vibr77/AppleIIDiskIIStm32F411/doc/controllercard/Apple-1-616-130-12-Apple-II-LIron-3-5-Unidisk-Floppy-Disk-Drive-Interface-Card_94765__16121.jpg

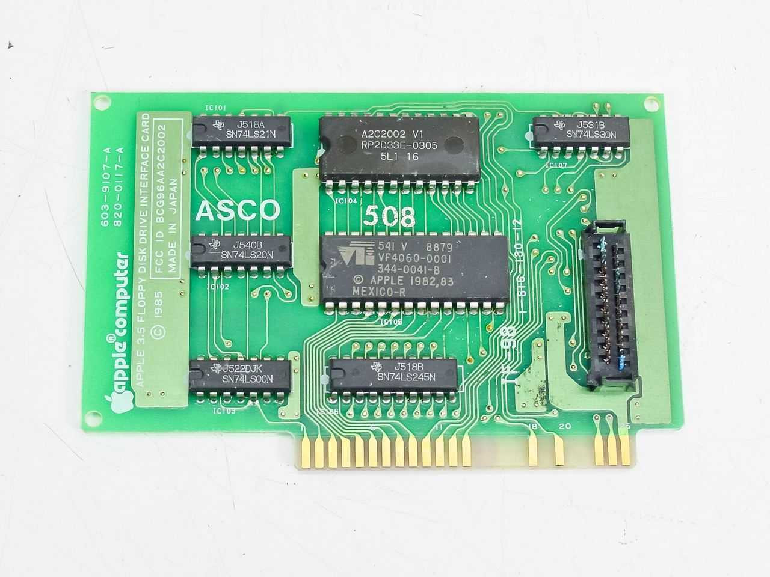
doc/controllercard/Apple-1-616-130-12-Apple-II-LIron-3-5-Unidisk-Floppy-Disk-Drive-Interface-Card_94765__16121.jpg
