vibr77/AppleIIDiskIIStm32F411/doc/controllercard/Disk-II-interface.jpg

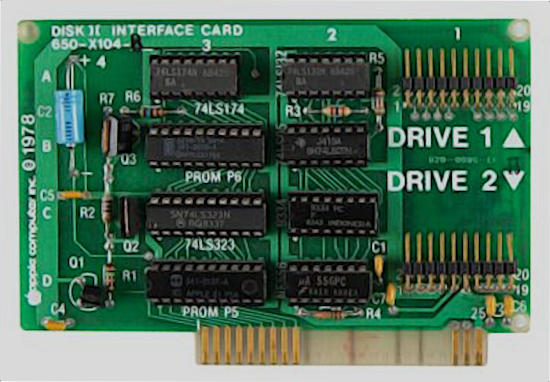
doc/controllercard/Disk-II-interface.jpg
