vibr77/AppleIIDiskIIStm32F411/doc/controllercard/grapplerminus.jpg

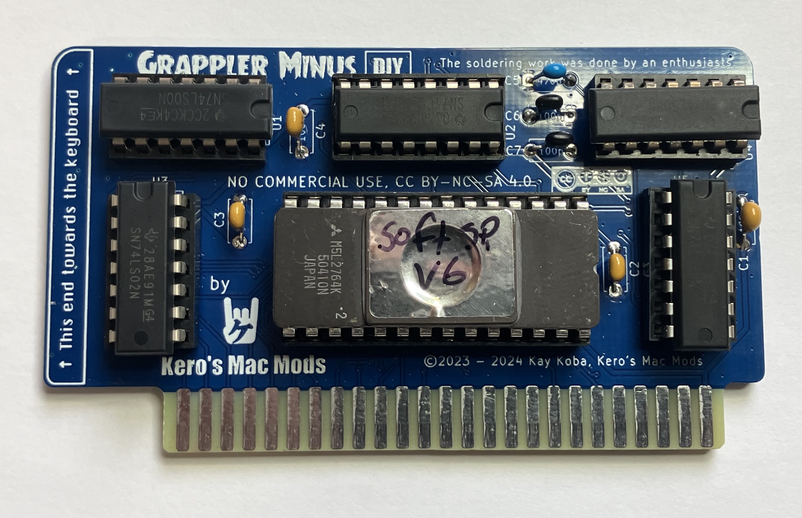
doc/controllercard/grapplerminus.jpg
