vibr77/AppleIIDiskIIStm32F411/doc/controllercard/yellowstone-270.png

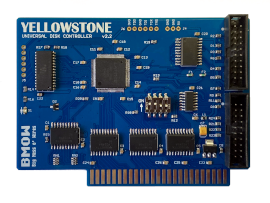
doc/controllercard/yellowstone-270.png
