vibr77/AppleIIDiskIIStm32F411/documentation/resources/IMG_1727-retouched-transparent_1_e6c90fae-1d42-45fb-9aed-f4f2a7baa5a6_1500x.png.webp

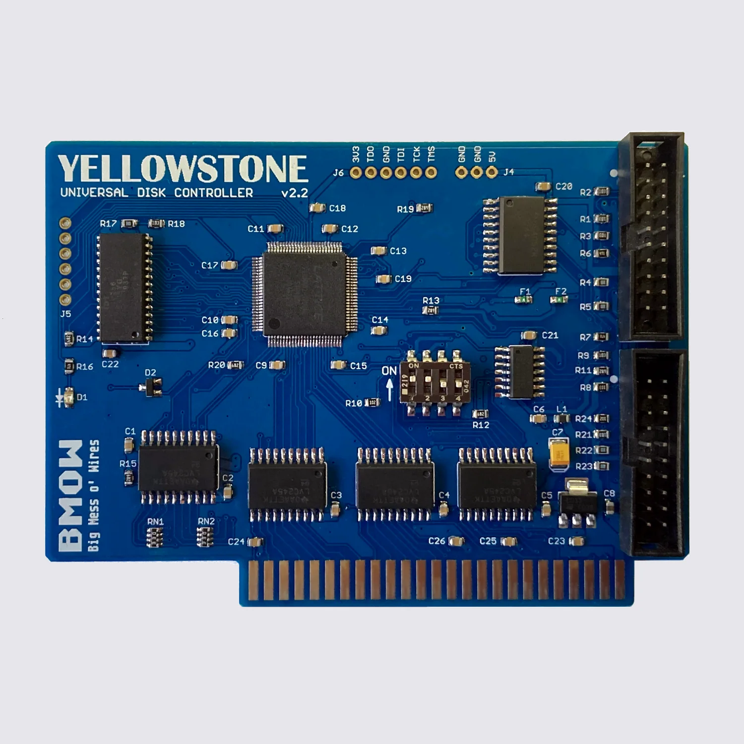
documentation/resources/IMG_1727-retouched-transparent_1_e6c90fae-1d42-45fb-9aed-f4f2a7baa5a6_1500x.png.webp
