vibr77/AppleIIDiskIIStm32F411/hardware/12085_buzzer/Image1.png

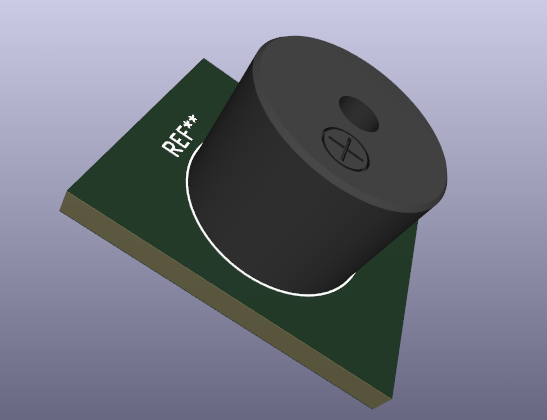
hardware/12085_buzzer/Image1.png
