vibr77/AppleIIDiskIIStm32F411/resources/CASE.jpeg

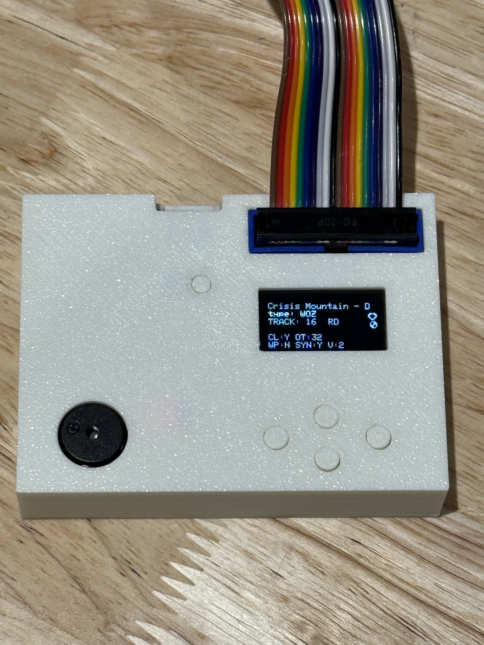
resources/CASE.jpeg
