vibr77/AppleIIDiskIIStm32F411/resources/PCB_REV_1_FILELST.jpeg

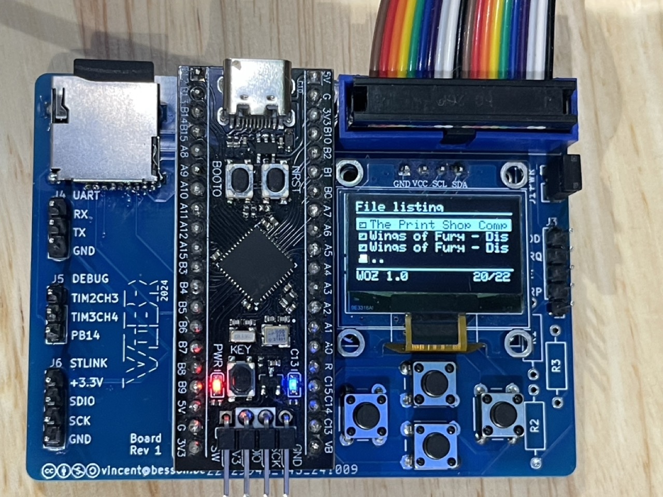
resources/PCB_REV_1_FILELST.jpeg
