vibr77/AppleIIDiskIIStm32F411/resources/STLINK.jpg

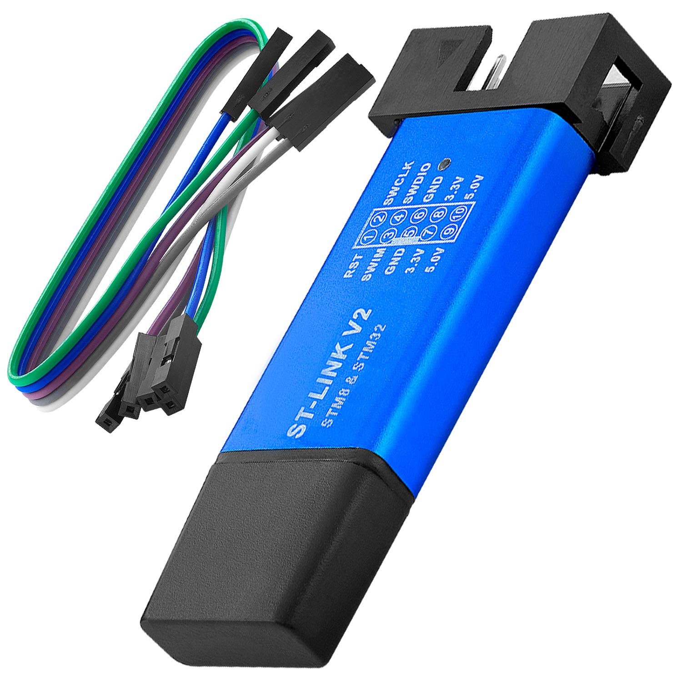
resources/STLINK.jpg
