vibr77/AppleIIDiskIIStm32F411/3DPrintCase/v4/SmartDiskII top v4.3mf

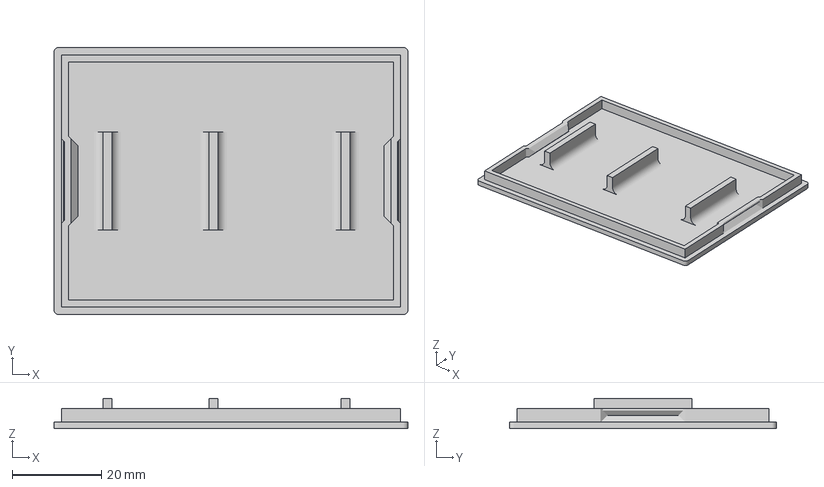
[picture p32: CAD file, 2025-01-04]
3DPrintCase/v4/SmartDiskII top v4.3mf
79.3 x 59.8 x 6.80 mm
