vibr77/AppleIIDiskIIStm32F411/hardware/stm32f411-stm32f401-black-pill-1.snapshot.5/Black Pill/STM32F4 Chip.FCStd

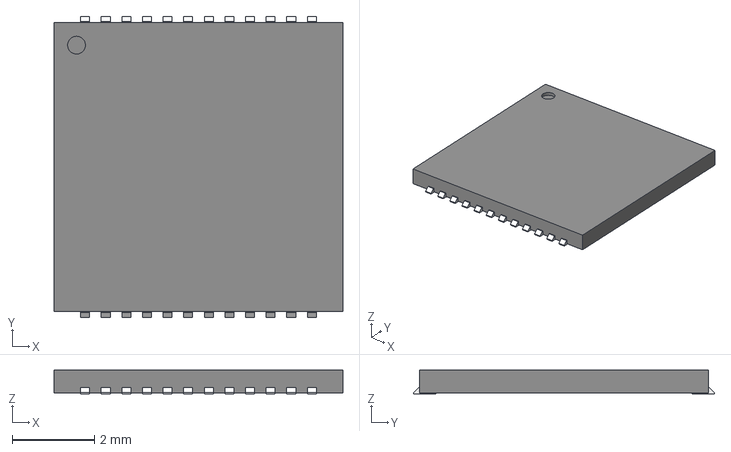
[picture p33: CAD file, 2026-02-05]
hardware/stm32f411-stm32f401-black-pill-1.snapshot.5/Black Pill/STM32F4 Chip.FCStd
7.00 x 7.30 x 0.57 mm
