vibr77/AppleIIDiskIIStm32F411/3DPrintCase/v4/SmartDiskII button reset v4.3mf

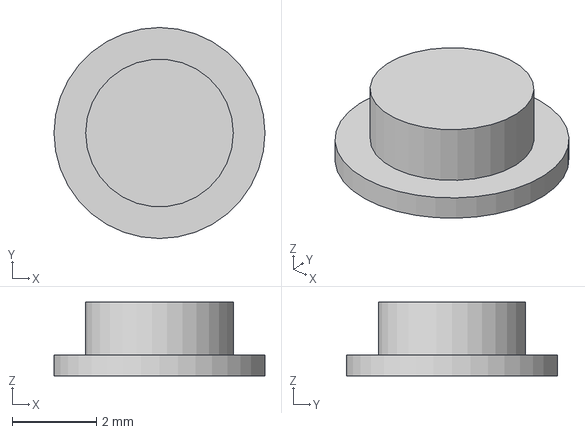
[picture p34: CAD file, 2024-12-24]
3DPrintCase/v4/SmartDiskII button reset v4.3mf
5.00 x 5.00 x 1.75 mm
