vibr77/AppleIIDiskIIStm32F411/hardware/stm32f411-stm32f401-black-pill-1.snapshot.5/Black Pill/Step File.FCStd

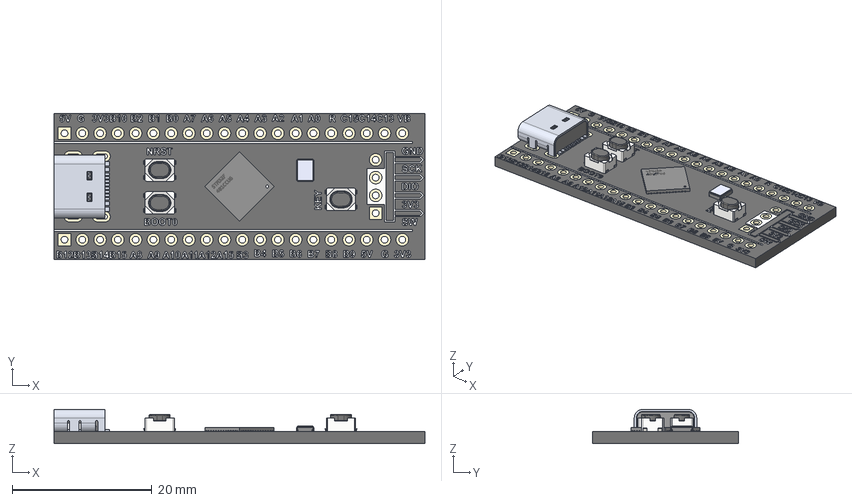
[picture p35: CAD file, 2026-02-05]
hardware/stm32f411-stm32f401-black-pill-1.snapshot.5/Black Pill/Step File.FCStd
53.0 x 20.9 x 4.92 mm
USB Type C Port (SMD Type) v1
USB Type C Port (SMD Type) v002
USB Type C Port (SMD Type) v003
USB Type C Port (SMD Type) v004
USB Type C Port (SMD Type) v005
USB Type C Port (SMD Type) v006
USB Type C Port (SMD Type) v007
USB Type C Port (SMD Type) v008
USB Type C Port (SMD Type) v009
USB Type C Port (SMD Type) v010
USB Type C Port (SMD Type) v011
USB Type C Port (SMD Type) v012
USB Type C Port (SMD Type) v013
USB Type C Port (SMD Type) v014
USB Type C Port (SMD Type) v015
USB Type C Port (SMD Type) v016
USB Type C Port (SMD Type) v017
USB Type C Port (SMD Type) v018
USB Type C Port (SMD Type) v019
USB Type C Port (SMD Type) v020
USB Type C Port (SMD Type) v021
USB Type C Port (SMD Type) v022
USB Type C Port (SMD Type) v023
USB Type C Port (SMD Type) v024
PTS810 SJK 250 SMTR LFS--3DModel-STEP-1 v2
PTS810 SJK 250 SMTR LFS--3DModel-STEP-1 v003
PTS810 SJK 250 SMTR LFS--3DModel-STEP-1 v004
PTS810 SJK 250 SMTR LFS--3DModel-STEP-1 v005
PTS810 SJK 250 SMTR LFS--3DModel-STEP-1 v006
PTS810 SJK 250 SMTR LFS--3DModel-STEP-1 v007
PTS810 SJK 250 SMTR LFS--3DModel-STEP-1 v008
PTS810 SJK 250 SMTR LFS--3DModel-STEP-1 v010
PTS810 SJK 250 SMTR LFS--3DModel-STEP-1 v011
PTS810 SJK 250 SMTR LFS--3DModel-STEP-1 v012
PTS810 SJK 250 SMTR LFS--3DModel-STEP-1 v013
PTS810 SJK 250 SMTR LFS--3DModel-STEP-1 v014
PTS810 SJK 250 SMTR LFS--3DModel-STEP-1 v015
PTS810 SJK 250 SMTR LFS--3DModel-STEP-1 v016
PTS810 SJK 250 SMTR LFS--3DModel-STEP-1 v2(Mirror)
PTS810 SJK 250 SMTR LFS--3DModel-STEP-1 v2(Mirror)001
PTS810 SJK 250 SMTR LFS--3DModel-STEP-1 v2(Mirror)002
PTS810 SJK 250 SMTR LFS--3DModel-STEP-1 v2(Mirror)003
PTS810 SJK 250 SMTR LFS--3DModel-STEP-1 v2(Mirror)004
PTS810 SJK 250 SMTR LFS--3DModel-STEP-1 v2(Mirror)005
PTS810 SJK 250 SMTR LFS--3DModel-STEP-1 v2(Mirror)006
STM32F411CEU6 v2
STM32F411CEU6 v003
STM32F411CEU6 v004
STM32F411CEU6 v005
STM32F411CEU6 v006
STM32F411CEU6 v007
STM32F411CEU6 v008
STM32F411CEU6 v009
STM32F411CEU6 v010
STM32F411CEU6 v011
STM32F411CEU6 v012
STM32F411CEU6 v013
STM32F411CEU6 v014
STM32F411CEU6 v015
STM32F411CEU6 v016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
