vibr77/AppleIIDiskIIStm32F411/3DPrintCase/v4/SmartDiskII button .3mf

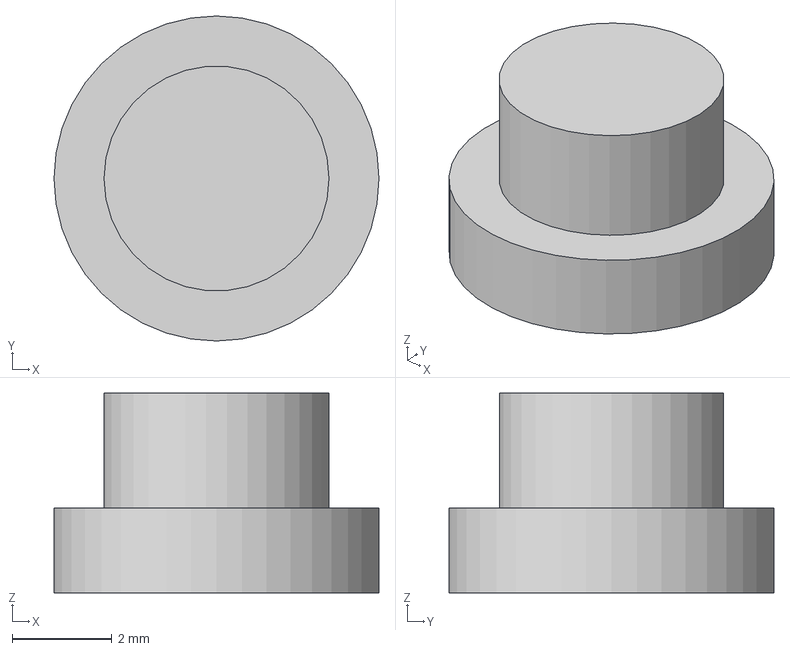
[picture p36: CAD file, 2024-12-24]
3DPrintCase/v4/SmartDiskII button .3mf
6.50 x 6.50 x 4.00 mm
