vibr77/AppleIIDiskIIStm32F411/hardware/stm32f411-stm32f401-black-pill-1.snapshot.5/Black Pill/Diode 2.FCStd

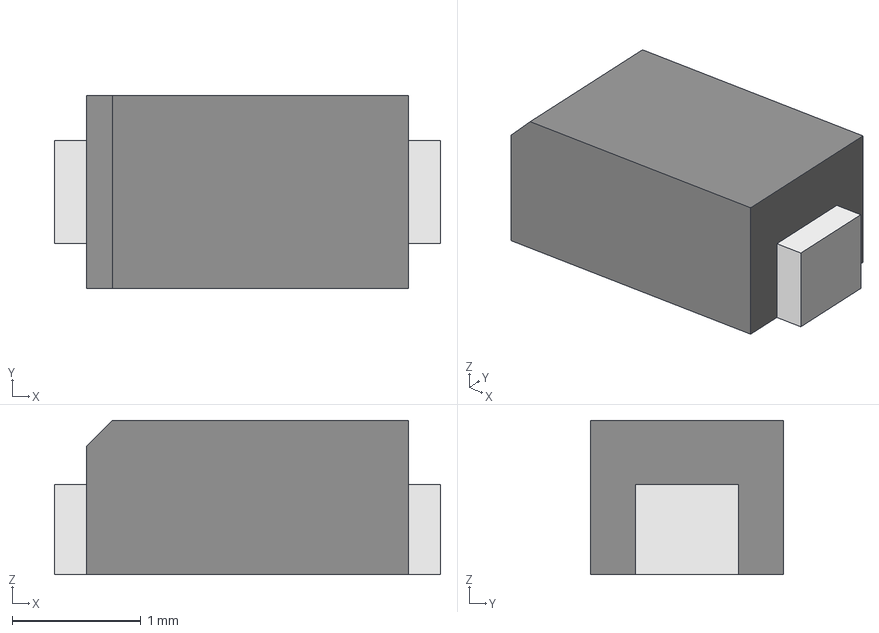
[picture p37: CAD file, 2026-02-05]
hardware/stm32f411-stm32f401-black-pill-1.snapshot.5/Black Pill/Diode 2.FCStd
3.00 x 1.50 x 1.20 mm
Body001 (Mirror #1)
