vibr77/AppleIIDiskIIStm32F411/hardware/stm32f411-stm32f401-black-pill-1.snapshot.5/Black Pill/Surface Mount Transistor.FCStd

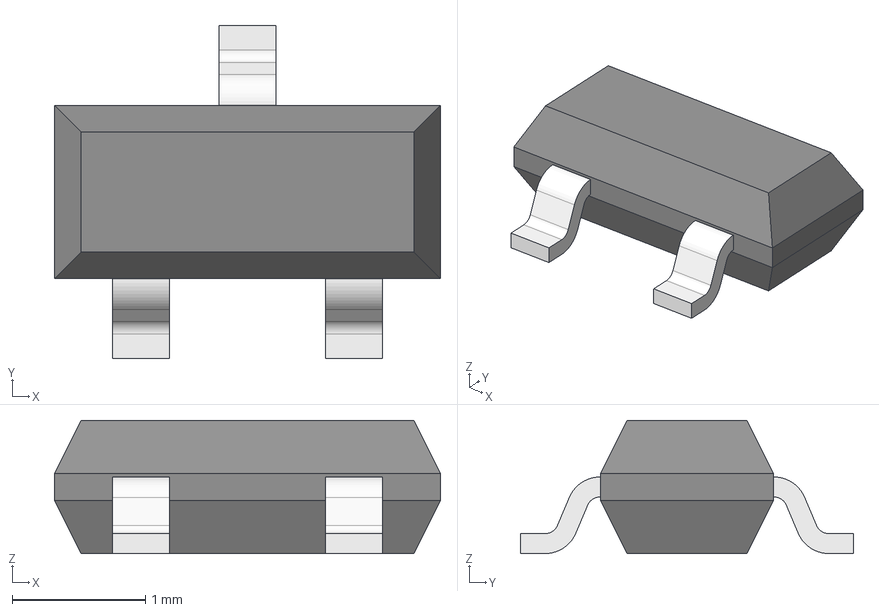
[picture p38: CAD file, 2026-02-05]
hardware/stm32f411-stm32f401-black-pill-1.snapshot.5/Black Pill/Surface Mount Transistor.FCStd
2.90 x 2.50 x 1.00 mm
