vibr77/AppleIIDiskIIStm32F411/hardware/stm32f411-stm32f401-black-pill-1.snapshot.5/Black Pill/1x20 Male Header.FCStd

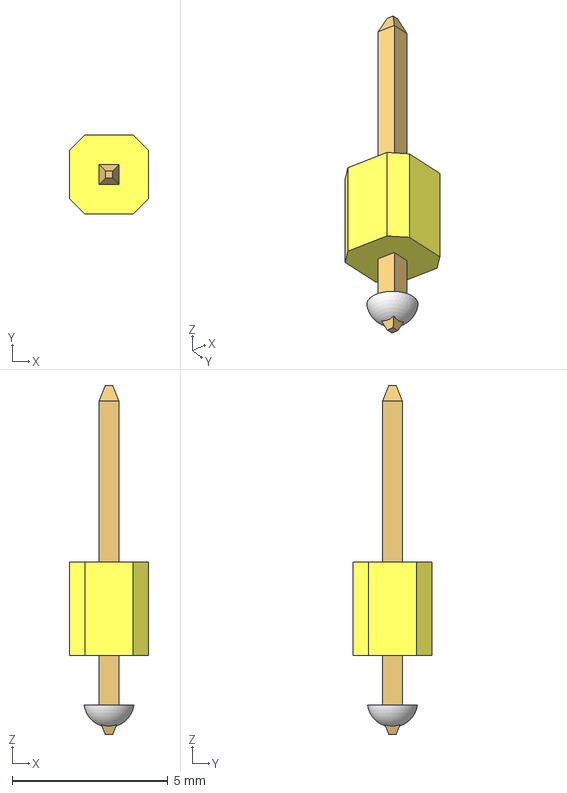
[picture p39: CAD file, 2026-02-05]
hardware/stm32f411-stm32f401-black-pill-1.snapshot.5/Black Pill/1x20 Male Header.FCStd
2.54 x 2.54 x 11.2 mm
