vibr77/AppleIIDiskIIStm32F411/hardware/stm32f411-stm32f401-black-pill-1.snapshot.5/Black Pill/0603 Capacitor.FCStd

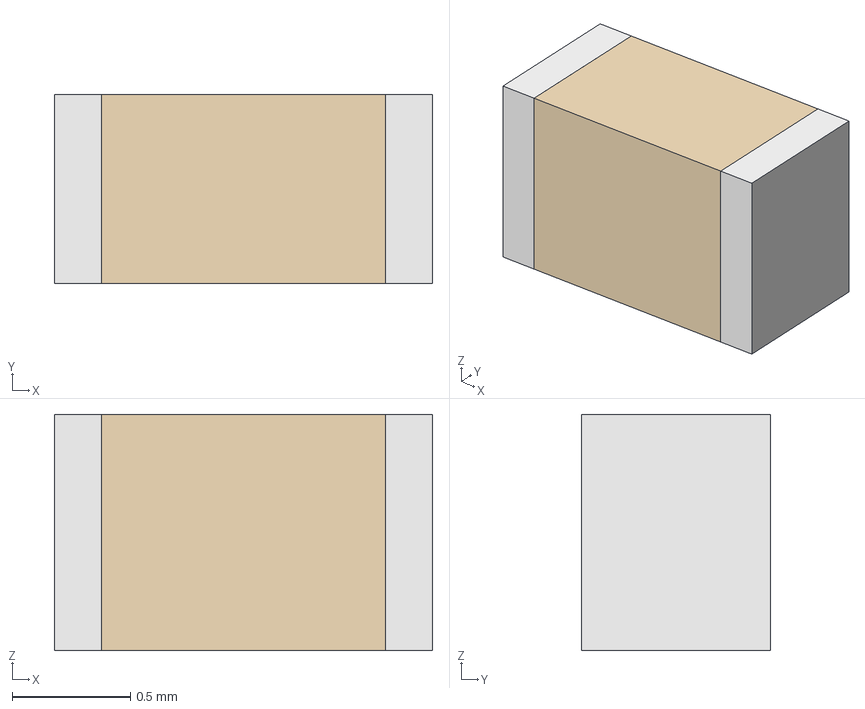
[picture p40: CAD file, 2026-02-05]
hardware/stm32f411-stm32f401-black-pill-1.snapshot.5/Black Pill/0603 Capacitor.FCStd
1.60 x 0.8 x 1.00 mm
Body001 (Mirror #1)
