vibr77/AppleIIDiskIIStm32F411/hardware/stm32f411-stm32f401-black-pill-1.snapshot.5/Black Pill/Crystal 1.FCStd

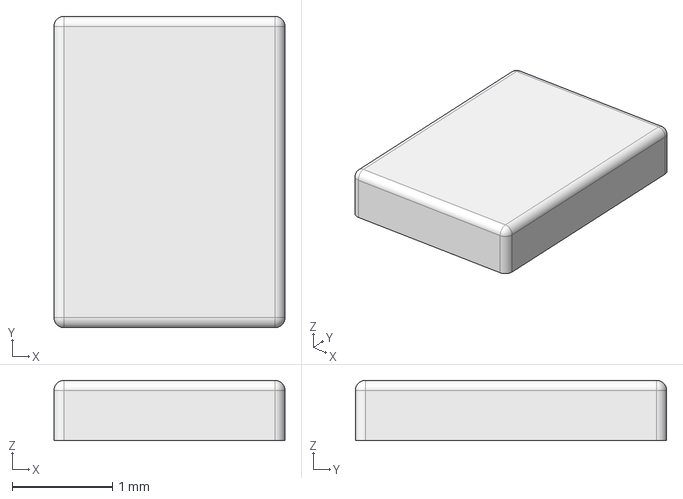
[picture p41: CAD file, 2026-02-05]
hardware/stm32f411-stm32f401-black-pill-1.snapshot.5/Black Pill/Crystal 1.FCStd
2.30 x 3.10 x 0.6 mm
