vibr77/AppleIIDiskIIStm32F411/hardware/stm32f411-stm32f401-black-pill-1.snapshot.5/Black Pill/0603 Resistor.FCStd

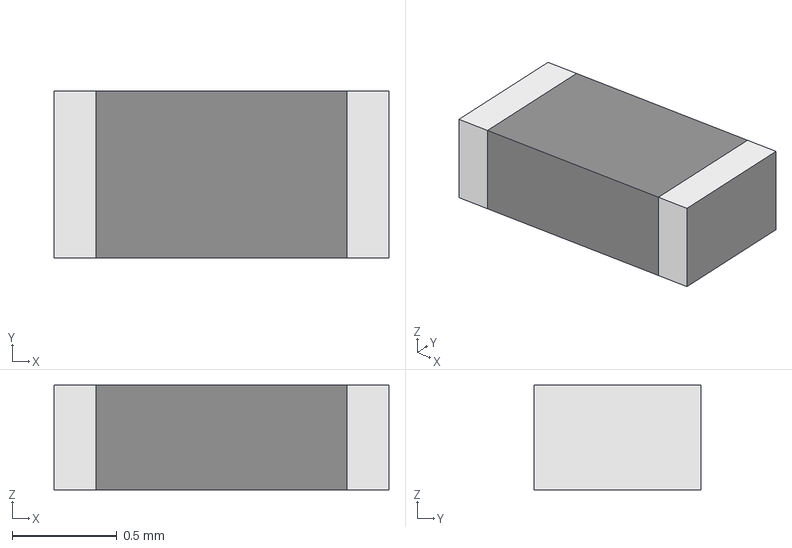
[picture p42: CAD file, 2026-02-05]
hardware/stm32f411-stm32f401-black-pill-1.snapshot.5/Black Pill/0603 Resistor.FCStd
1.60 x 0.8 x 0.5 mm
Body001 (Mirror #1)
