vibr77/AppleIIDiskIIStm32F411/hardware/stm32f411-stm32f401-black-pill-1.snapshot.5/Black Pill/0402 Resistor.FCStd

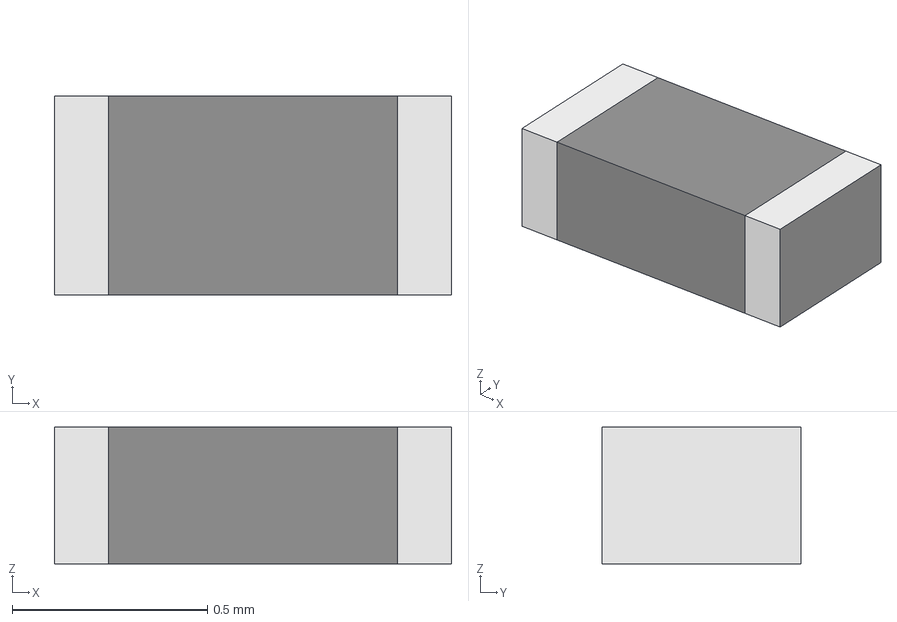
[picture p43: CAD file, 2026-02-05]
hardware/stm32f411-stm32f401-black-pill-1.snapshot.5/Black Pill/0402 Resistor.FCStd
1.02 x 0.508 x 0.35 mm
Body001 (Mirror #1)
