vibr77/AppleIIDiskIIStm32F411/hardware/stm32f411-stm32f401-black-pill-1.snapshot.5/Black Pill/0402 Capacitor.FCStd

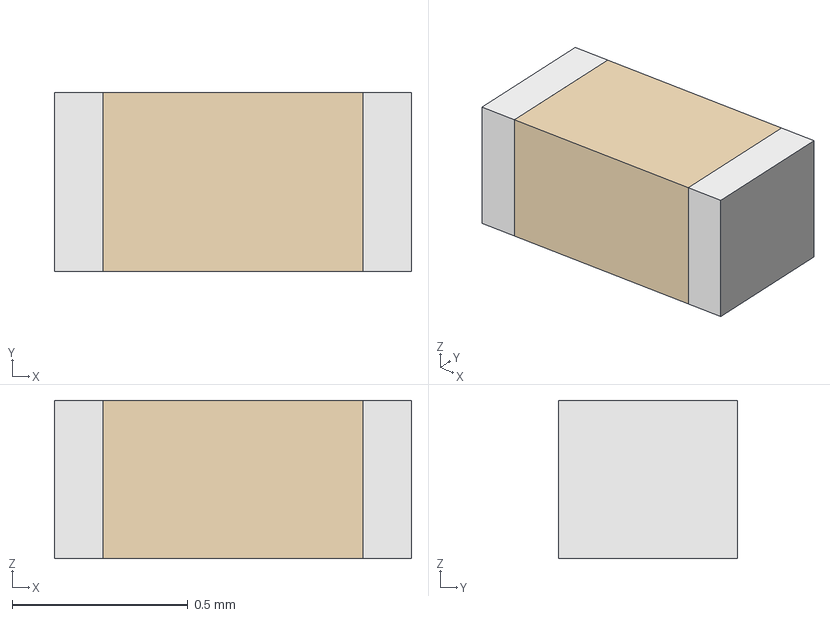
[picture p44: CAD file, 2026-02-05]
hardware/stm32f411-stm32f401-black-pill-1.snapshot.5/Black Pill/0402 Capacitor.FCStd
1.02 x 0.508 x 0.45 mm
Body001 (Mirror #1)
