vibr77/AppleIIDiskIIStm32F411/hardware/stm32f411-stm32f401-black-pill-1.snapshot.5/Black Pill/1x4 Right Angle Male Header.FCStd

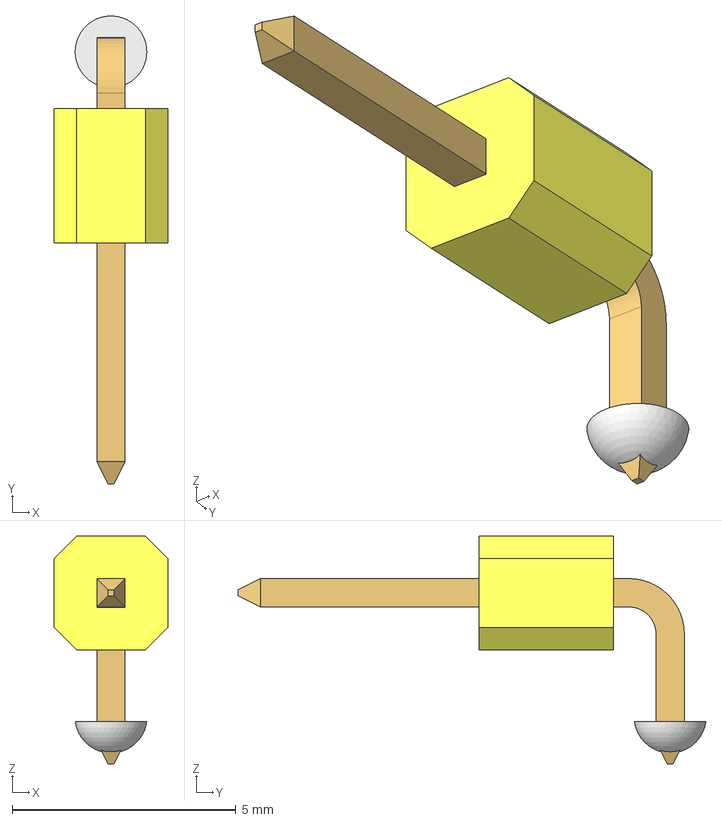
[picture p45: CAD file, 2026-02-05]
hardware/stm32f411-stm32f401-black-pill-1.snapshot.5/Black Pill/1x4 Right Angle Male Header.FCStd
2.54 x 10.4 x 5.08 mm
