vibr77/AppleIIDiskIIStm32F411/hardware/stm32f411-stm32f401-black-pill-1.snapshot.5/Black Pill/Tac Switch.FCStd

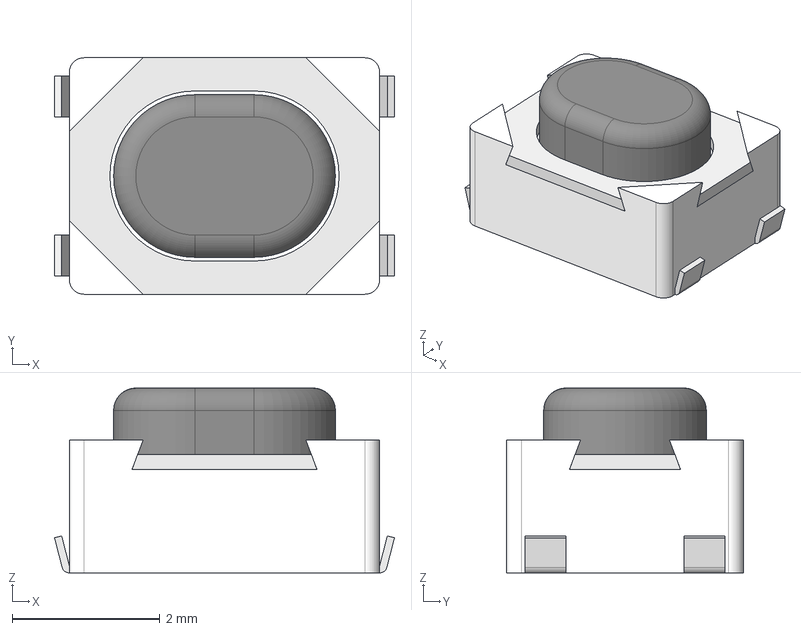
[picture p47: CAD file, 2026-02-05]
hardware/stm32f411-stm32f401-black-pill-1.snapshot.5/Black Pill/Tac Switch.FCStd
4.60 x 3.20 x 2.50 mm
Body002 (Mirror #1)
