vibr77/AppleIIDiskIIStm32F411/Contributed/Build/Bildschirmfoto 2025-02-22 um 20.39.24.png

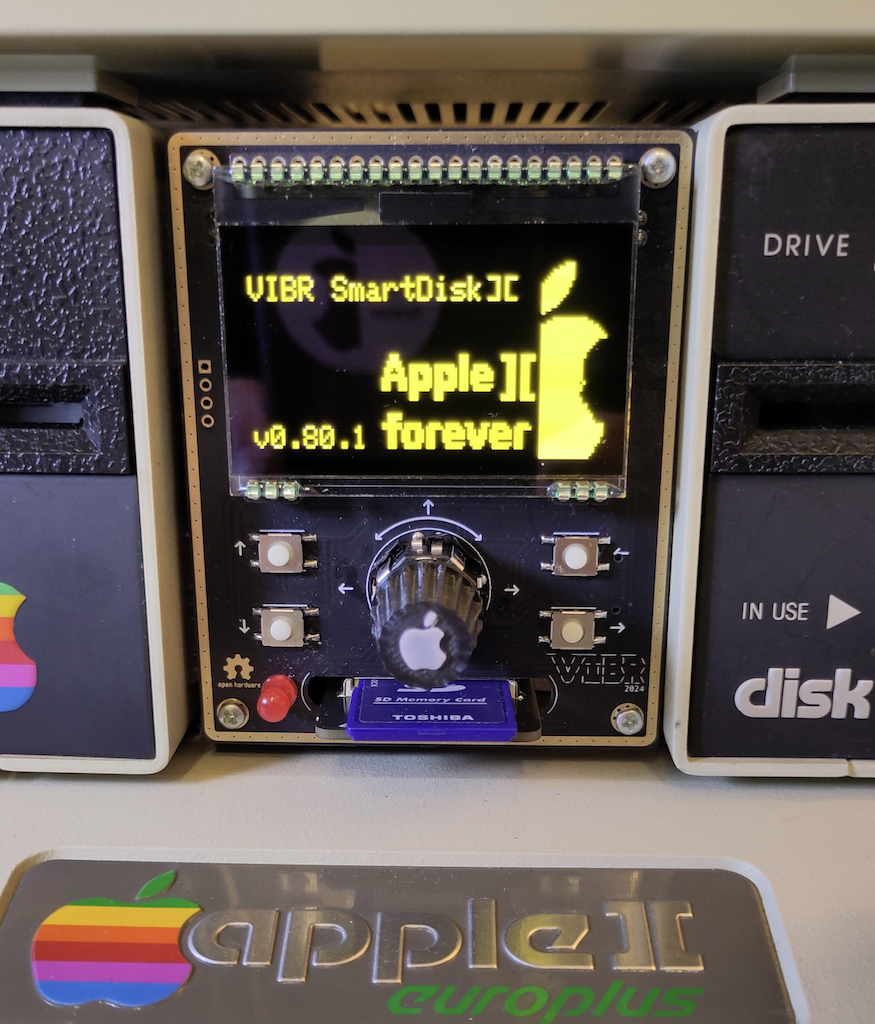
Contributed/Build/Bildschirmfoto 2025-02-22 um 20.39.24.png
