vibr77/AppleIIDiskIIStm32F411/Core/Inc/driver_nic.h

#ifndef nic_h
#define nic_h

#include <stdbool.h>
#include <stdio.h>
#include <string.h>
#include <stdint.h>

int getNicTrackFromPh(int phtrack);
unsigned int getNicTrackSize(int trk);
long getNicSDAddr(int trk,int block,int csize, long database);
enum STATUS getNicTrackBitStream(int trk,unsigned char * buffer);
enum STATUS mountNicFile(char * filename);
enum STATUS createNewDiskNic(char * filename);

#endif
