vibr77/AppleIIDiskIIStm32F411/smartloader.c

unsigned char smartloader_bin[] = {
  0x01, 0xad, 0xb4, 0x08, 0xc9, 0x08, 0xd0, 0x03, 0x20, 0x58, 0x08, 0xa5,
  0x27, 0xc9, 0x09, 0xd0, 0x0e, 0xa5, 0x2b, 0x4a, 0x4a, 0x4a, 0x4a, 0x09,
  0xc0, 0x85, 0x3f, 0xa9, 0x5c, 0x85, 0x3e, 0xae, 0xb5, 0x08, 0xe0, 0x10,
  0xf0, 0x2f, 0xee, 0xb5, 0x08, 0xae, 0xb4, 0x08, 0xe0, 0x00, 0xf0, 0x18,
  0xce, 0xb4, 0x08, 0xbd, 0xa4, 0x08, 0x85, 0x3d, 0xad, 0xb7, 0x08, 0x85,
  0x27, 0xce, 0xb7, 0x08, 0xa6, 0x2b, 0xad, 0xb4, 0x08, 0x6c, 0x3e, 0x00,
  0xa9, 0x47, 0x8d, 0xb7, 0x08, 0xa2, 0x0f, 0x8e, 0xb4, 0x08, 0x4c, 0x33,
  0x08, 0x4c, 0x00, 0x40, 0x20, 0x58, 0xfc, 0xa2, 0x0e, 0xa0, 0x00, 0x20,
  0xb8, 0x08, 0xa2, 0xff, 0x86, 0x32, 0xa2, 0x92, 0xa0, 0x08, 0x20, 0xd5,
  0x08, 0xa2, 0x22, 0xa0, 0x17, 0x20, 0xb8, 0x08, 0xa2, 0x9e, 0xa0, 0x08,
  0x20, 0xd5, 0x08, 0xa2, 0x00, 0xa0, 0x01, 0x20, 0xb8, 0x08, 0xa0, 0x28,
  0x20, 0xc1, 0x08, 0xa0, 0x14, 0x20, 0xb8, 0x08, 0xa0, 0x28, 0x20, 0xc1,
  0x08, 0x60, 0xd3, 0xcd, 0xc1, 0xd2, 0xd4, 0xcc, 0xcf, 0xc1, 0xc4, 0xc5,
  0xd2, 0x00, 0xf6, 0xb0, 0xae, 0xb4, 0xb3, 0x00, 0x00, 0x0d, 0x0b, 0x09,
  0x07, 0x05, 0x03, 0x01, 0x0e, 0x0c, 0x0a, 0x08, 0x06, 0x04, 0x02, 0x0f,
  0x08, 0x00, 0x00, 0xbf, 0x48, 0x98, 0x86, 0x24, 0x20, 0x5b, 0xfb, 0x68,
  0x60, 0xa9, 0xdf, 0x20, 0xed, 0xfd, 0x88, 0xd0, 0xf8, 0x60, 0x48, 0xe9,
  0xe0, 0xb0, 0x02, 0x68, 0x60, 0x68, 0x29, 0xdf, 0x60, 0x86, 0x80, 0x84,
  0x81, 0xa0, 0x00, 0xb1, 0x80, 0xf0, 0x0b, 0x20, 0xca, 0x08, 0x20, 0xf0,
  0xfd, 0xc8, 0xb1, 0x80, 0xd0, 0xf5, 0x60, 0x00, 0x00, 0x00, 0x00, 0x00,
  0x00, 0x00, 0x00, 0x00, 0x00, 0x00, 0x00, 0x00, 0x00, 0x00, 0x00, 0x00,
  0x00, 0x00, 0x00, 0x00, 0xa2, 0x00, 0xa0, 0x02, 0x88, 0xb1, 0x3e, 0x4a,
  0x3e, 0x00, 0xbc, 0x4a, 0x3e, 0x00, 0xbc, 0x99, 0x00, 0xbb, 0xe8, 0xe0,
  0x56, 0x90, 0xed, 0xa2, 0x00, 0x98, 0xd0, 0xe8, 0xa2, 0x55, 0xbd, 0x00,
  0xbc, 0x29, 0x3f, 0x9d, 0x00, 0xbc, 0xca, 0x10, 0xf5, 0x60, 0x38, 0x86,
  0x27, 0x8e, 0x78, 0x06, 0xbd, 0x8d, 0xc0, 0xbd, 0x8e, 0xc0, 0x30, 0x7c,
  0xad, 0x00, 0xbc, 0x85, 0x26, 0xa9, 0xff, 0x9d, 0x8f, 0xc0, 0x1d, 0x8c,
  0xc0, 0x48, 0x68, 0xea, 0xa0, 0x04, 0x48, 0x68, 0x20, 0xb9, 0xb8, 0x88,
  0xd0, 0xf8, 0xa9, 0xd5, 0x20, 0xb8, 0xb8, 0xa9, 0xaa, 0x20, 0xb8, 0xb8,
  0xa9, 0xad, 0x20, 0xb8, 0xb8, 0x98, 0xa0, 0x56, 0xd0, 0x03, 0xb9, 0x00,
  0xbc, 0x59, 0xff, 0xbb, 0xaa, 0xbd, 0x29, 0xba, 0xa6, 0x27, 0x9d, 0x8d,
  0xc0, 0xbd, 0x8c, 0xc0, 0x88, 0xd0, 0xeb, 0xa5, 0x26, 0xea, 0x59, 0x00,
  0xbb, 0xaa, 0xbd, 0x29, 0xba, 0xae, 0x78, 0x06, 0x9d, 0x8d, 0xc0, 0xbd,
  0x8c, 0xc0, 0xb9, 0x00, 0xbb, 0xc8, 0xd0, 0xea, 0xaa, 0xbd, 0x29, 0xba,
  0xa6, 0x27, 0x20, 0xbb, 0xb8, 0xa9, 0xde, 0x20, 0xb8, 0xb8, 0xa9, 0xaa,
  0x20, 0xb8, 0xb8, 0xa9, 0xeb, 0x20, 0xb8, 0xb8, 0xa9, 0xff, 0x20, 0xb8,
  0xb8, 0xbd, 0x8e, 0xc0, 0xbd, 0x8c, 0xc0, 0x60, 0x18, 0x48, 0x68, 0x9d,
  0x8d, 0xc0, 0x1d, 0x8c, 0xc0, 0x60, 0xa0, 0x00, 0xa2, 0x56, 0xca, 0x30,
  0xfb, 0xb9, 0x00, 0xbb, 0x5e, 0x00, 0xbc, 0x2a, 0x5e, 0x00, 0xbc, 0x2a,
  0x91, 0x3e, 0xc8, 0xc4, 0x26, 0xd0, 0xeb, 0x60, 0xa0, 0x20, 0x88, 0xf0,
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
};
unsigned int smartloader_bin_len = 8192;
